YasodGinige/ElderBot/GSMcode_SMS/GSM_only_test.ino

/* This code works with sim800l and a push button
 * Press the button to send a simple SMS/Text to a specified phone number
 * Refer to www.SurtrTech.com for more details 
 */

#include <SoftwareSerial.h>

SoftwareSerial sim800l(2, 3); // RX,TX for Arduino and for the module it's TXD RXD, they should be inverted

#define button1 7 //Button pin, on the other pin it's wired with GND

bool button_State; //Button state


void setup()
{
 
  pinMode(button1, INPUT_PULLUP); //The button is always on HIGH level, when pressed it goes LOW
  sim800l.begin(9600);   //Module baude rate, this is on max, it depends on the version
  Serial.begin(9600);   
  delay(1000);
  SendSMS();
}
 
void loop()
{
  

  button_State = digitalRead(button1);   //We are constantly reading the button State
 
  if (button_State == LOW) {            //And if it's pressed
    Serial.println("Button pressed");   //Shows this message on the serial monitor
    delay(200);                         //Small delay to avoid detecting the button press many times
    
    SendSMS();                          //And this function is called

 }
 
  if (sim800l.available()){            //Displays on the serial monitor if there's a communication from the module
    Serial.write(sim800l.read()); 
  }
}
 
void SendSMS()
{
  Serial.println("Sending SMS...");               //Show this message on serial monitor
  sim800l.println("AT+CMGF=0\"\r");                   //Set the module to SMS mode
  delay(100);
  sim800l.println("AT+CMGS=\"+94773604959\"\r");  //Your phone number don't forget to include your country code, example +212123456789"
  delay(500);
  sim800l.println("sim800l is working");       //This is the text to send to the phone number, don't make it too long or you have to modify the SoftwareSerial buffer
  delay(500);
  sim800l.println((char)26);// (required according to the datasheet)
  delay(500);
  sim800l.println();
  Serial.println("Text Sent.");
  delay(500);

}
 
